jtsiomb/sgikbd/fw/src/scantbl.h

#ifndef SCANTBL_H_
#define SCANTBL_H_

#define KEYMAP_NORMAL_SIZE	(sizeof keymap_normal / sizeof *keymap_normal)

/* converts a normal (non-extended) PS/2 scancode to an SGI keycode */
static unsigned char keymap_normal[] = {
	0xff, 0x5e, 0xff, 0x5a, 0x58, 0x56, 0x57, 0x61,		/* 00 - 07: - f9 - f5 f3 f1 f2 f12 */
	0xff, 0x5f, 0x5d, 0x5b, 0x59, 0x08, 0x36, 0xff,		/* 08 - 0f: - f10 f8 f6 f4 tab ` - */
	0xff, 0x53, 0x05, 0xff, 0x02, 0x09, 0x07, 0xff,		/* 10 - 17: - lalt lshift - lctrl Q 1 - */
	0xff, 0xff, 0x13, 0x0b, 0x0a, 0x0f, 0x0d, 0xff,		/* 18 - 1f: - - Z S A W 2 - */
	0xff, 0x1b, 0x14, 0x11, 0x10, 0x15, 0x0e, 0xff,		/* 20 - 27: - C X D E 4 3 - */
	0xff, 0x52, 0x1c, 0x12, 0x18, 0x17, 0x16, 0xff,		/* 28 - 2f: - space V F T R 5 - */
	0xff, 0x24, 0x23, 0x1a, 0x19, 0x1f, 0x1d, 0xff,		/* 30 - 37: - N B H G Y 6 - */
	0xff, 0xff, 0x2b, 0x21, 0x20, 0x1e, 0x25, 0xff,		/* 38 - 3f: - - M J U 7 8 - */
	0xff, 0x2c, 0x22, 0x27, 0x28, 0x2d, 0x26, 0xff,		/* 40 - 47: - , K I O 0 9 - */
	0xff, 0x33, 0x34, 0x29, 0x2a, 0x2f, 0x2e, 0xff,		/* 48 - 4f: - . / L ; P minus - */
	0xff, 0xff, 0x31, 0xff, 0x30, 0x35, 0xff, 0xff,		/* 50 - 57: - - ' - [ = - - */
	0x03, 0x04, 0x32, 0x37, 0xff, 0x38, 0xff, 0xff,		/* 58 - 5f: caps rshift enter ] - \ - - */
	0xff, 0xff, 0xff, 0xff, 0xff, 0xff, 0x3c, 0xff,		/* 60 - 67: - - - - - - backsp - */
	0xff, 0x39, 0xff, 0x3e, 0x42, 0xff, 0xff, 0xff,		/* 68 - 6f: - KP1 - KP4 KP7 - - - */
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
	0xff, 0x68, 0xff, 0x48, 0x66, 0xff, 0xff, 0xff,		/* 68 - 6f: - end - left home - - - */
	0x65, 0x3d, 0x49, 0xff, 0x4f, 0x50, 0xff, 0xff,		/* 70 - 77: ins del down - right up - - */
	0xff, 0xff, 0x69, 0xff, 0xff, 0x67, 0xff, 0xff		/* 78 - 7f: - - pgdown - - pgup - - */
};

#endif	/* SCANTBL_H_ */
